Ezecarp36/BoverGroup-Proyecto-LeviatanX/Libreriaskicad(2023)/3d/3d/NRF24L01.step

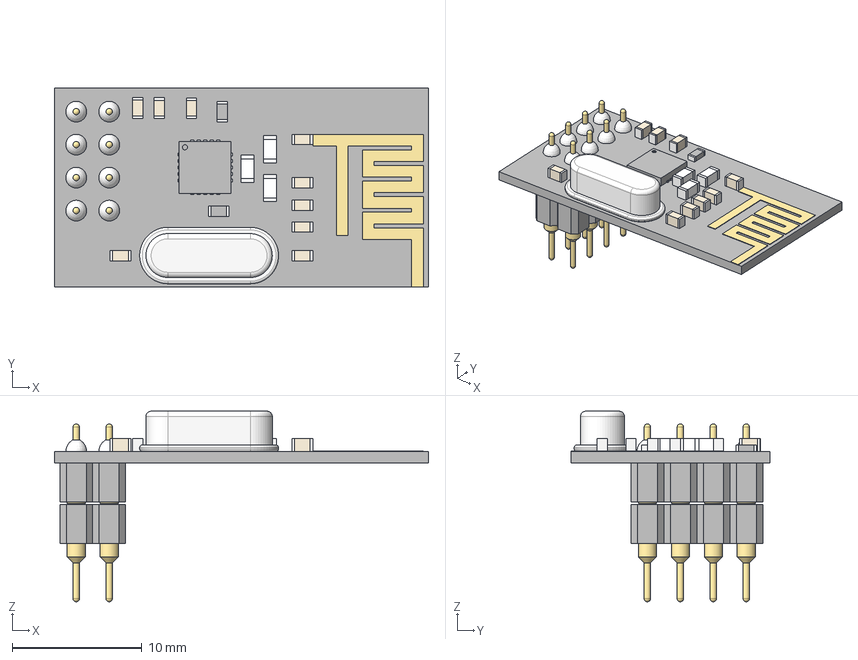
[picture p19: CAD file, 2023-04-25]
Libreriaskicad(2023)/3d/3d/NRF24L01.step
28.8 x 15.3 x 14.7 mm
1x4 Male Header 2_001
1x4 Male Header 2_002
1x4 Female Header_001
1x4 Female Header_002
0603 Resistor_001
0603 Capacitor_001
0603 Resistor_002
0603 Capacitor_002
0603 Capacitor_003
0603 Capacitor_004
0603 Capacitor_005
0603 Capacitor_006
0603 Capacitor_007
0603 Capacitor_008
0603 Capacitor_009
White SM Capacitor_001
White SM Capacitor_002
White SM Capacitor_003
Crystal 16MHz_001
NRF Chip_001
