Ezecarp36/BoverGroup-Proyecto-LeviatanX/Libreriaskicad(2023)/3d/3d/jst-sh-smd-connectors-1.snapshot.4/SHR-xxV-S-B/SHR-09V-S-B.STEP

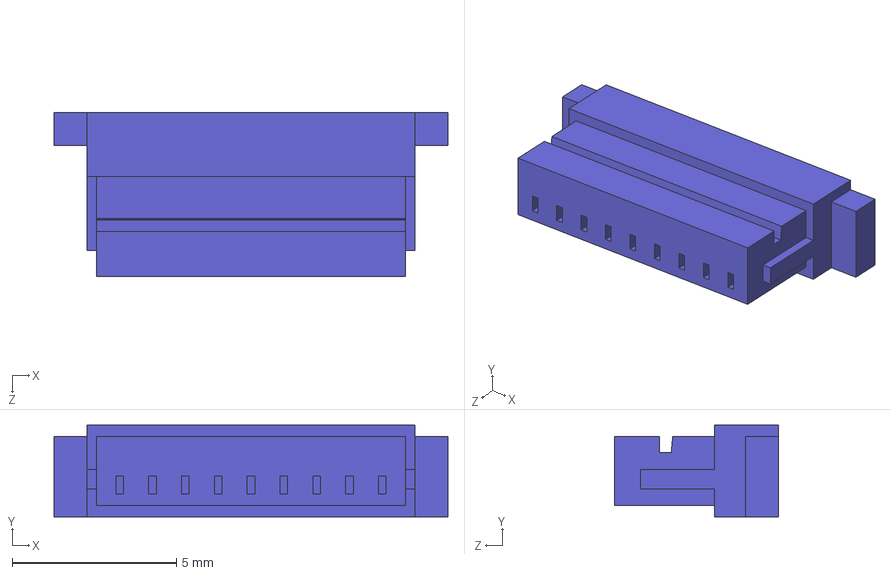
[picture p21: CAD file, 2023-04-25]
Libreriaskicad(2023)/3d/3d/jst-sh-smd-connectors-1.snapshot.4/SHR-xxV-S-B/SHR-09V-S-B.STEP
12.0 x 2.80 x 5.00 mm
