Ezecarp36/BoverGroup-Proyecto-LeviatanX/Libreriaskicad(2023)/3d/3d/jst-sh-smd-connectors-1.snapshot.4/SHR-xxV-S/SHR-02V-S.STEP

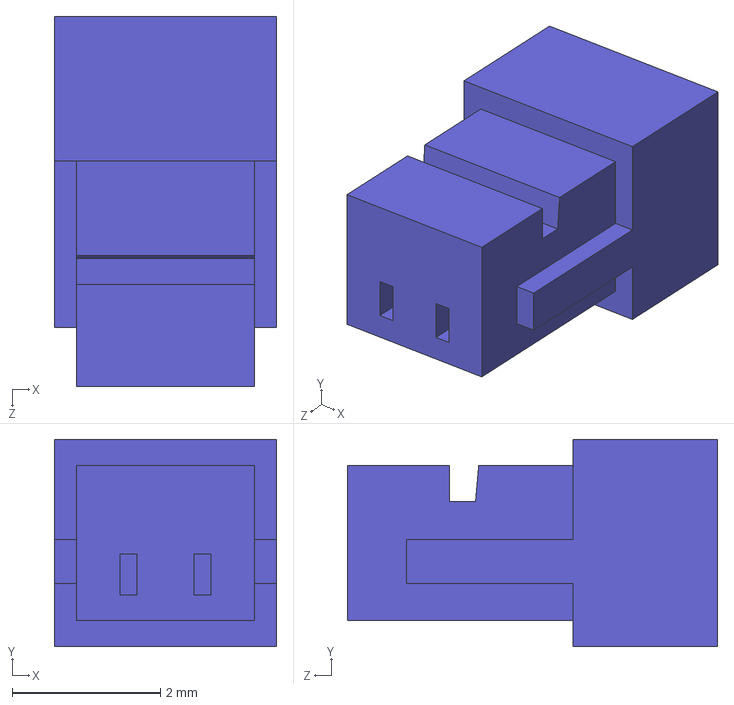
[picture p22: CAD file, 2023-04-25]
Libreriaskicad(2023)/3d/3d/jst-sh-smd-connectors-1.snapshot.4/SHR-xxV-S/SHR-02V-S.STEP
3.00 x 2.80 x 5.00 mm
