Ezecarp36/BoverGroup-Proyecto-LeviatanX/Libreriaskicad(2023)/3d/3d/jst-sh-smd-connectors-1.snapshot.4/SHR-xxV-S-B/SHR-03V-S-B.STEP

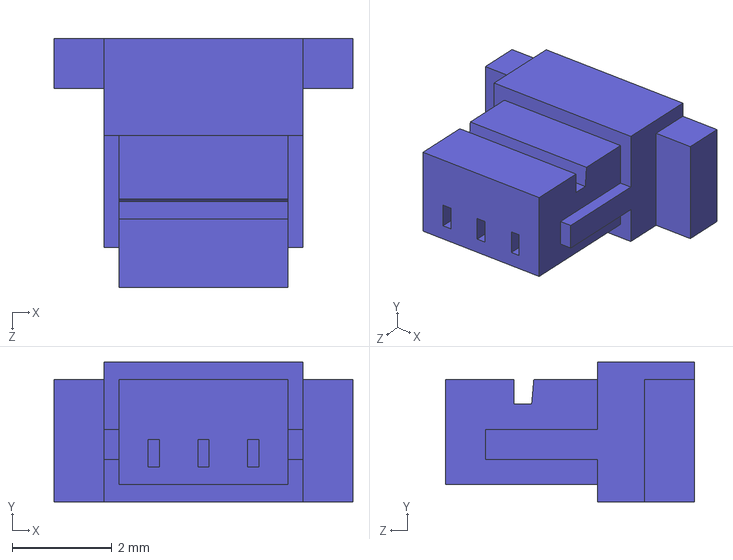
[picture p25: CAD file, 2023-04-25]
Libreriaskicad(2023)/3d/3d/jst-sh-smd-connectors-1.snapshot.4/SHR-xxV-S-B/SHR-03V-S-B.STEP
6.00 x 2.80 x 5.00 mm
