Ezecarp36/BoverGroup-Proyecto-LeviatanX/Libreriaskicad(2023)/3d/3d/jst-sh-smd-connectors-1.snapshot.4/SHR-xxV-S/SHR-11V-S.STEP

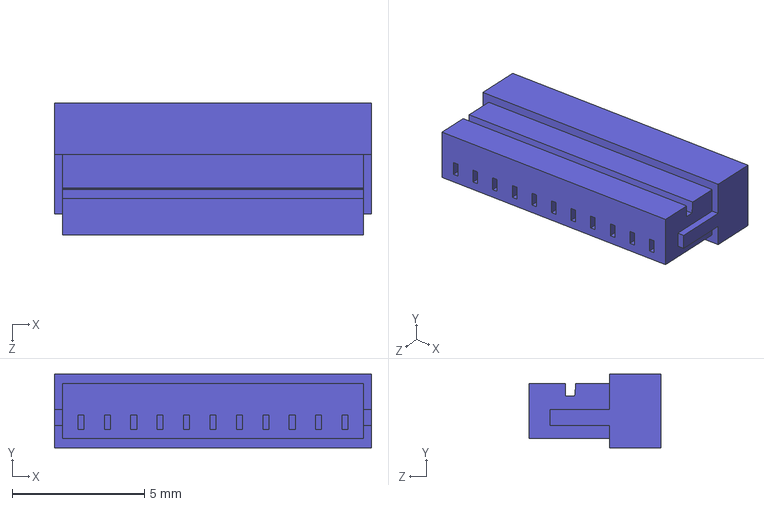
[picture p26: CAD file, 2023-04-25]
Libreriaskicad(2023)/3d/3d/jst-sh-smd-connectors-1.snapshot.4/SHR-xxV-S/SHR-11V-S.STEP
12.0 x 2.80 x 5.00 mm
