Ezecarp36/BoverGroup-Proyecto-LeviatanX/Libreriaskicad(2023)/3d/3d/jst-sh-smd-connectors-1.snapshot.4/SMxxB-SRSS-TB/SM03B-SRSS-TB.STEP

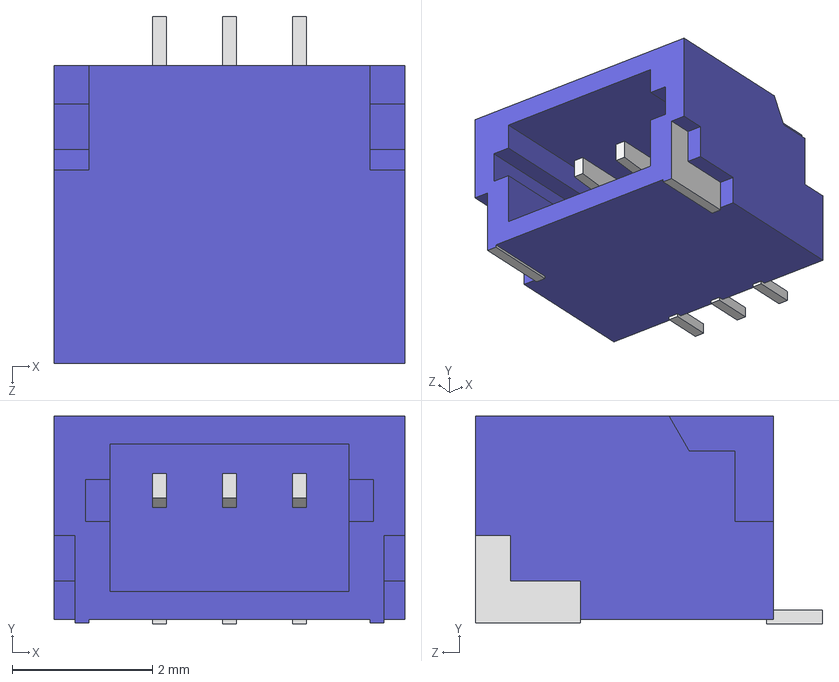
[picture p27: CAD file, 2023-04-25]
Libreriaskicad(2023)/3d/3d/jst-sh-smd-connectors-1.snapshot.4/SMxxB-SRSS-TB/SM03B-SRSS-TB.STEP
5.00 x 2.96 x 4.95 mm
