Ezecarp36/BoverGroup-Proyecto-LeviatanX/Libreriaskicad(2023)/3d/3d/jst-sh-smd-connectors-1.snapshot.4/SMxxB-SRSS-TB/SM15B-SRSS-TB.STEP

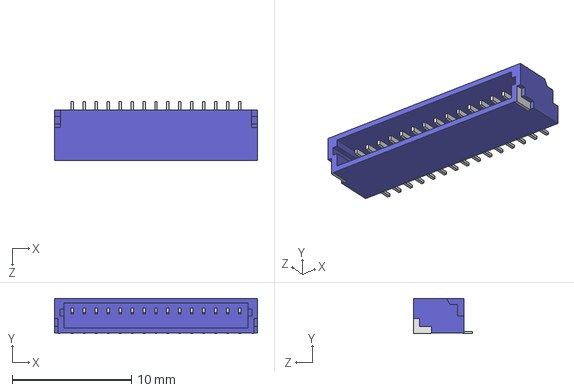
[picture p31: CAD file, 2023-04-25]
Libreriaskicad(2023)/3d/3d/jst-sh-smd-connectors-1.snapshot.4/SMxxB-SRSS-TB/SM15B-SRSS-TB.STEP
17.0 x 2.96 x 4.95 mm
