Ezecarp36/BoverGroup-Proyecto-LeviatanX/Libreriaskicad(2023)/3d/3d/jst-sh-smd-connectors-1.snapshot.4/BMxxB-SRSR-TB/BM11B-SRSS-TB.STEP

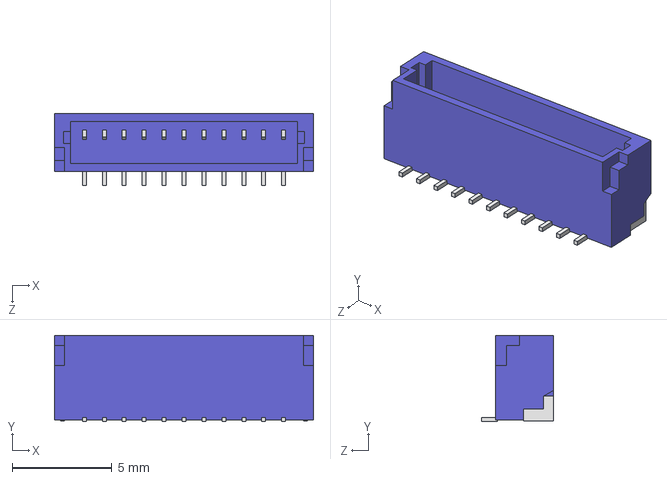
[picture p32: CAD file, 2023-04-25]
Libreriaskicad(2023)/3d/3d/jst-sh-smd-connectors-1.snapshot.4/BMxxB-SRSR-TB/BM11B-SRSS-TB.STEP
13.0 x 4.32 x 3.60 mm
