Ezecarp36/BoverGroup-Proyecto-LeviatanX/Software/PruebasMPU6050/CalibrarOffSets/CalibrarOffSets.ino

// Librerias I2C para controlar el mpu6050
// la libreria MPU6050.h necesita I2Cdev.h, I2Cdev.h necesita Wire.h
#include "I2Cdev.h"
#include "MPU6050.h"
#include "Wire.h"

// La dirección del MPU6050 puede ser 0x68 o 0x69, dependiendo 
// del estado de AD0. Si no se especifica, 0x68 estará implicito
MPU6050 sensor;

// Valores RAW (sin procesar) del acelerometro y giroscopio en los ejes x,y,z
int16_t ax, ay, az;
int16_t gx, gy, gz;

//Variables usadas por el filtro pasa bajos
long f_ax,f_ay, f_az;
int p_ax, p_ay, p_az;
long f_gx,f_gy, f_gz;
int p_gx, p_gy, p_gz;
int counter=0;

//Valor de los offsets
int ax_o,ay_o,az_o;
int gx_o,gy_o,gz_o;

void setup() {
  Serial.begin(115200);   //Iniciando puerto serial
  Wire.begin();           //Iniciando I2C  
  sensor.initialize();    //Iniciando el sensor

  if (sensor.testConnection()) Serial.println("Sensor iniciado correctamente");

  // Leer los offset los offsets anteriores
  ax_o=sensor.getXAccelOffset();
  ay_o=sensor.getYAccelOffset();
  az_o=sensor.getZAccelOffset();
  gx_o=sensor.getXGyroOffset();
  gy_o=sensor.getYGyroOffset();
  gz_o=sensor.getZGyroOffset();
  
  Serial.println("Offsets:");
  Serial.print(ax_o); Serial.print("\t"); 
  Serial.print(ay_o); Serial.print("\t"); 
  Serial.print(az_o); Serial.print("\t"); 
  Serial.print(gx_o); Serial.print("\t"); 
  Serial.print(gy_o); Serial.print("\t");
  Serial.print(gz_o); Serial.print("\t");
  Serial.println("\n Envie cualquier caracter para empezar la calibracion");  
  // Espera un caracter para empezar a calibrar
  while (true){if (Serial.available()) break;}  
  Serial.println("Calibrando, no mover IMU");  
  
}

void loop() {
  // Leer las aceleraciones y velocidades angulares
  sensor.getAcceleration(&ax, &ay, &az);
  sensor.getRotation(&gx, &gy, &gz);

  // Filtrar las lecturas
  f_ax = f_ax-(f_ax>>5)+ax;
  p_ax = f_ax>>5;

  f_ay = f_ay-(f_ay>>5)+ay;
  p_ay = f_ay>>5;

  f_az = f_az-(f_az>>5)+az;
  p_az = f_az>>5;

  f_gx = f_gx-(f_gx>>3)+gx;
  p_gx = f_gx>>3;

  f_gy = f_gy-(f_gy>>3)+gy;
  p_gy = f_gy>>3;

  f_gz = f_gz-(f_gz>>3)+gz;
  p_gz = f_gz>>3;

  //Cada 100 lecturas corregir el offset
  if (counter==100){
    //Mostrar las lecturas separadas por un [tab]
    Serial.print("promedio:"); Serial.print("\t");
    Serial.print(p_ax); Serial.print("\t");
    Serial.print(p_ay); Serial.print("\t");
    Serial.print(p_az); Serial.print("\t");
    Serial.print(p_gx); Serial.print("\t");
    Serial.print(p_gy); Serial.print("\t");
    Serial.println(p_gz);

    //Calibrar el acelerometro a 1g en el eje z (ajustar el offset)
    if (p_ax>0) ax_o--;
    else {ax_o++;}
    if (p_ay>0) ay_o--;
    else {ay_o++;}
    if (p_az-16384>0) az_o--;
    else {az_o++;}
    
    sensor.setXAccelOffset(ax_o);
    sensor.setYAccelOffset(ay_o);
    sensor.setZAccelOffset(az_o);

    //Calibrar el giroscopio a 0º/s en todos los ejes (ajustar el offset)
    if (p_gx>0) gx_o--;
    else {gx_o++;}
    if (p_gy>0) gy_o--;
    else {gy_o++;}
    if (p_gz>0) gz_o--;
    else {gz_o++;}
    
    sensor.setXGyroOffset(gx_o);
    sensor.setYGyroOffset(gy_o);
    sensor.setZGyroOffset(gz_o);    

    counter=0;
  }
  counter++;
}
