Ezecarp36/BoverGroup-Proyecto-LeviatanX/Software/Pruebas Componentes/PruebasNrfl2401/NRF24_Receptor/NRF24_Receptor.ino

#include <RF24.h>
#define CE_PIN 27
#define CSN_PIN 15

const byte thisSlaveAddress[5] = {'R', 'x', 'A', 'A', 'A'};

RF24 radio(CE_PIN, CSN_PIN);

char dataReceived[10]; // this must match dataToSend in the TX
bool newData = false;

//===========

void setup()
{

   Serial.begin(9600);
   delay(3000);
   Serial.println("SimpleRx Starting");
   radio.begin();
   radio.setDataRate( RF24_250KBPS );
   radio.openReadingPipe(1, thisSlaveAddress);
   radio.startListening();
}

//=============

void loop()
{
   getData();
   showData();
}

//==============

void getData()
{
   if ( radio.available() )
   {
      radio.read( &dataReceived, sizeof(dataReceived) );
      newData = true;
   }
}

void showData()
{
   if (newData == true)
   {
      Serial.print("Data received ");
      Serial.println(dataReceived);
      newData = false;
   }
}
